tux-friend/tux-cube/board_back_1.png

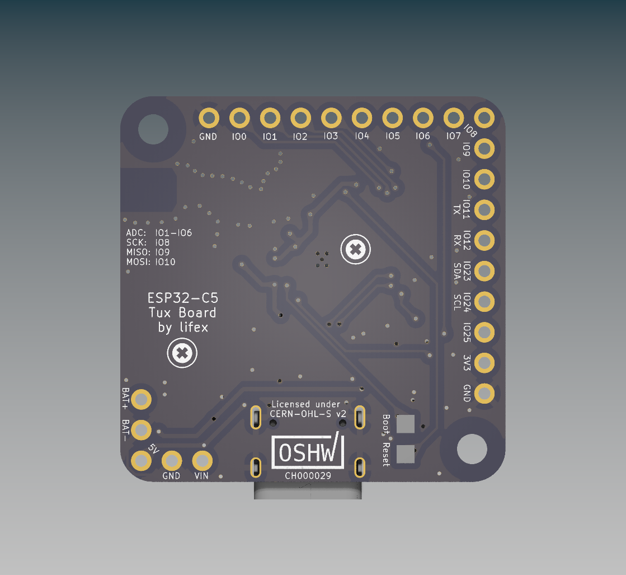
board_back_1.png
