tux-friend/tux-cube/board_front_1.png

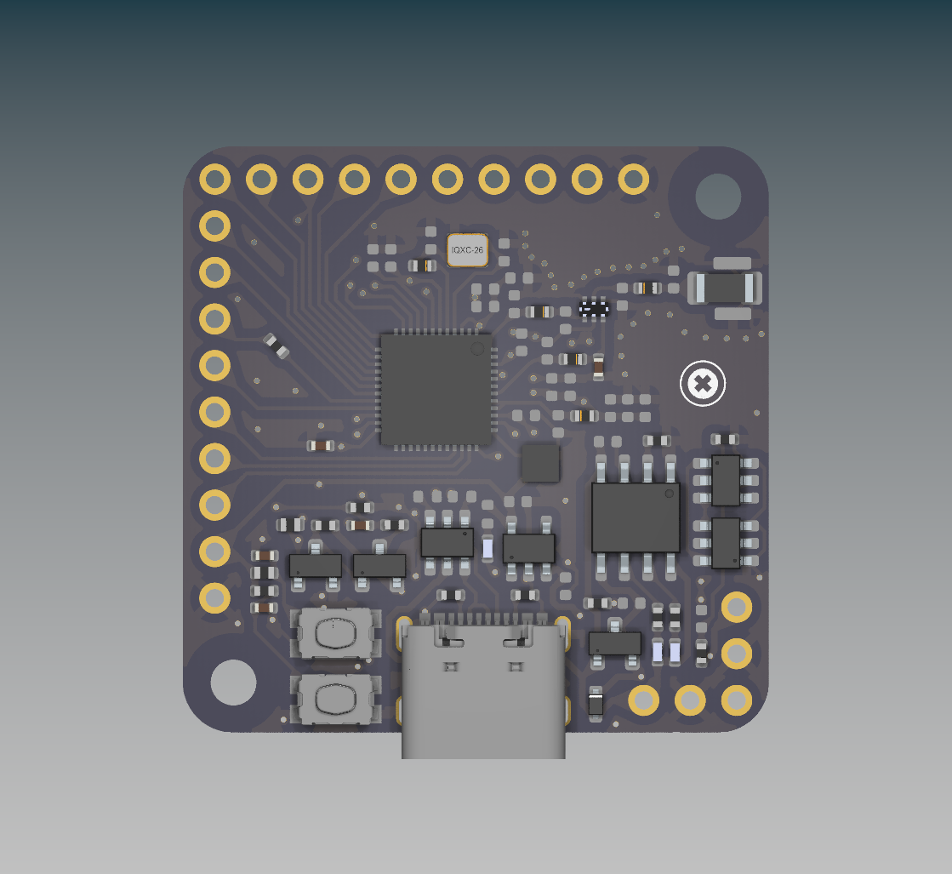
board_front_1.png
