tux-friend/tux-cube/tux3_prototype_1.jpg

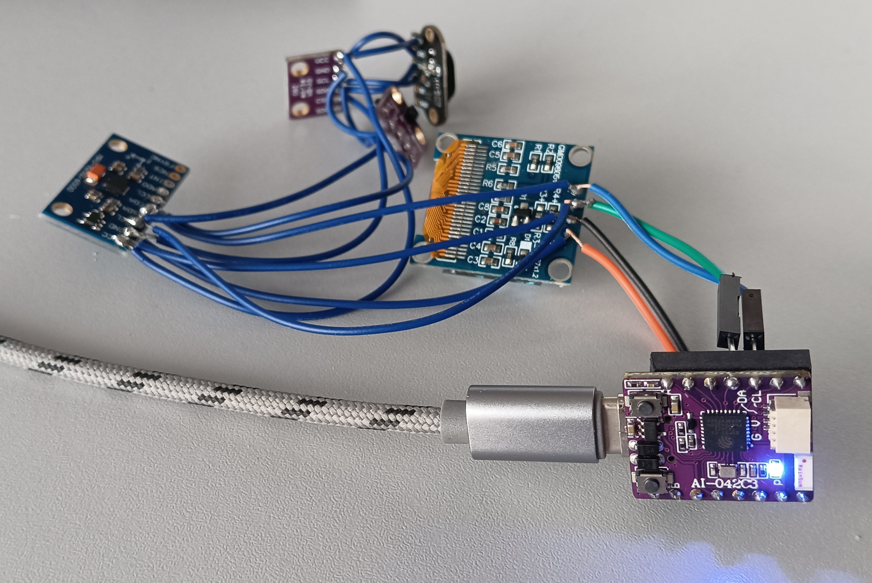
tux3_prototype_1.jpg
