tux-friend/tux-cube/tux3_prototype_2.jpg

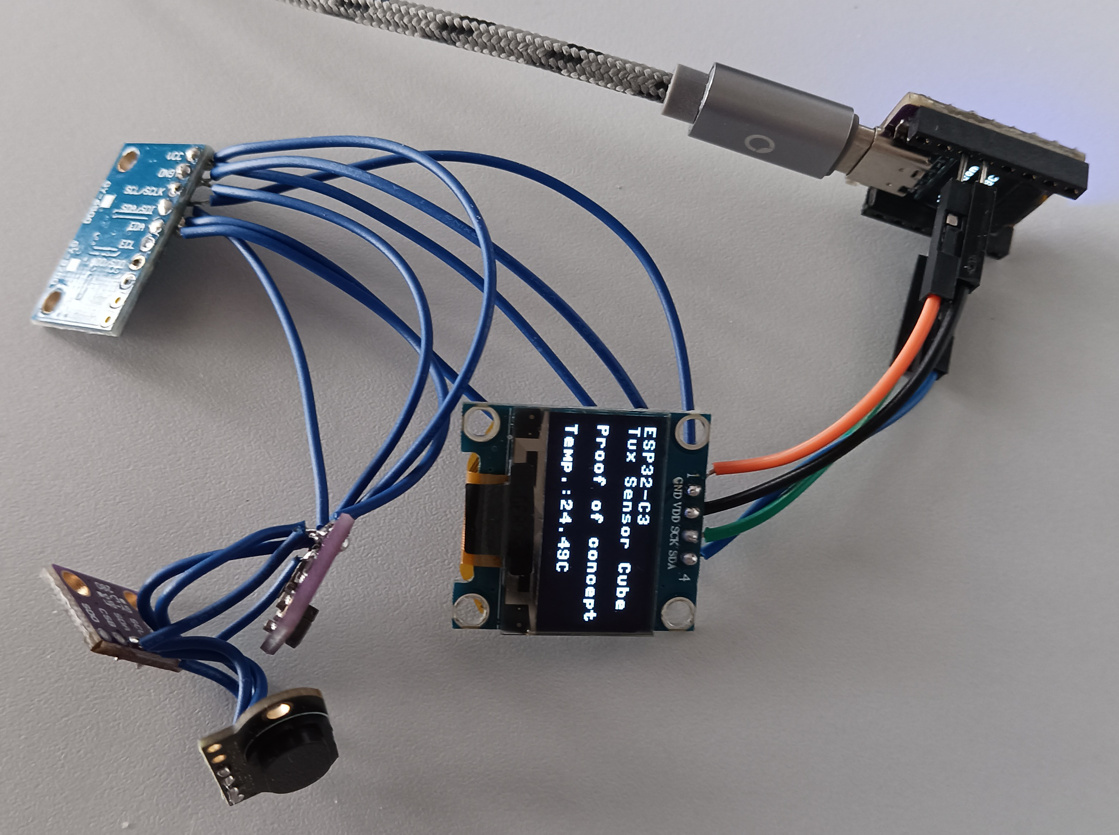
tux3_prototype_2.jpg
